RujulPawar/Encore/BuckConverterLtspice.asc

C1: cap; 6.6µ
C2: cap; 0.1nF
D1: diode
D2: diode; 1N4148
L1: ind; 100µ
M1: nmos; BSZ065N06LS5
M2: nmos; BSZ065N06LS5
R2: res; 100k
R3: res; 56k
R4: res; 1k
Rout: res; 1.15
U1: NE555
V1: voltage; 24v
V2: voltage; 5
Named nets: 0, Vo, Vs
.tran 0 21m 0 0.001m
